Fra4prg/ServoSimulator/pictures/20191102_115943.jpg

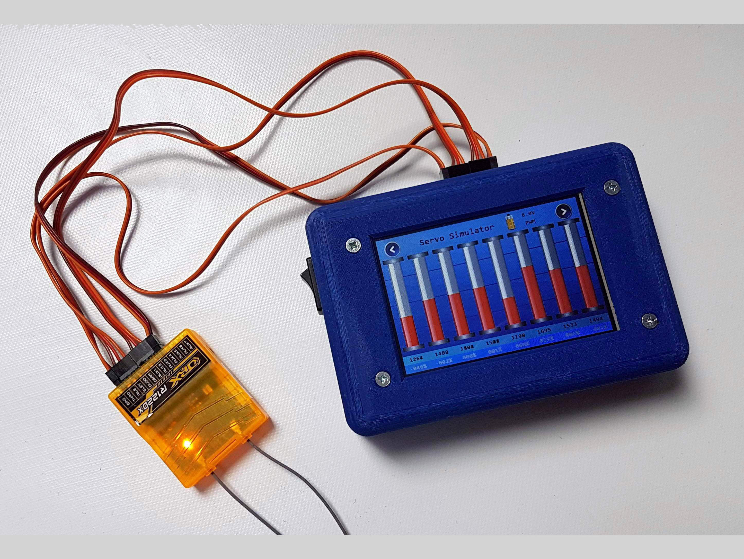
pictures/20191102_115943.jpg
