Fra4prg/ServoSimulator/pictures/20191102_115950.jpg

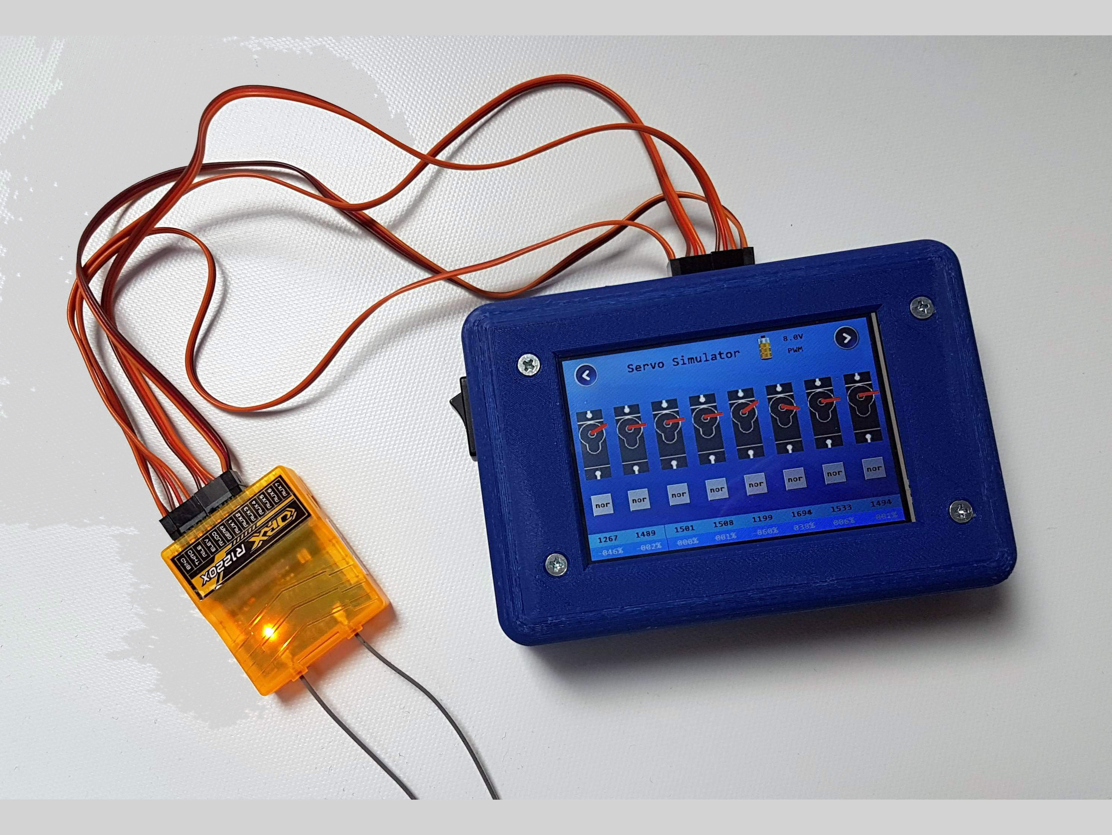
pictures/20191102_115950.jpg
