Fra4prg/ServoSimulator/pictures/20191102_120322.jpg

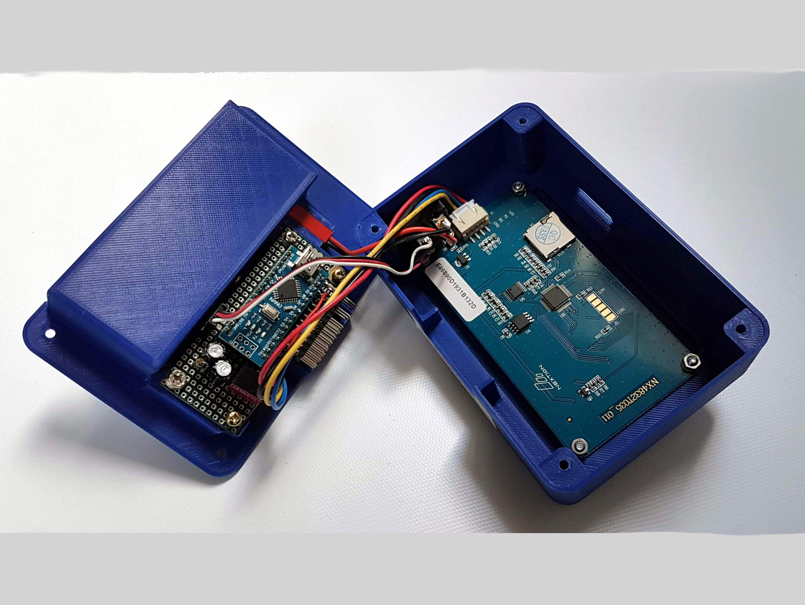
pictures/20191102_120322.jpg
