Fra4prg/ServoSimulator/pictures/20191102_122256.jpg

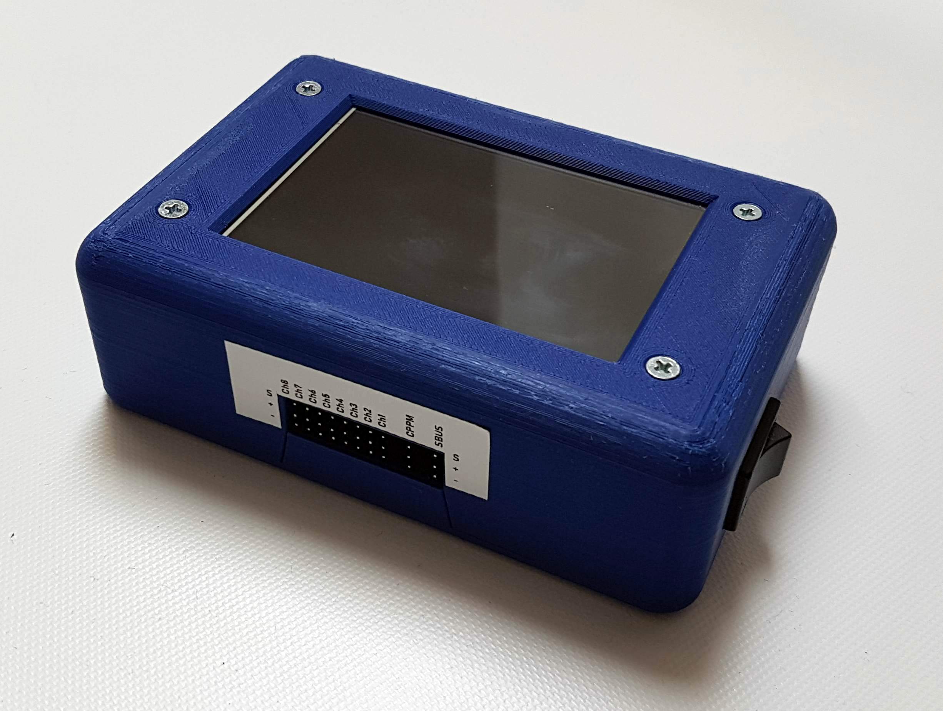
pictures/20191102_122256.jpg
