Fra4prg/ServoSimulator/pictures/20191102_122544.jpg

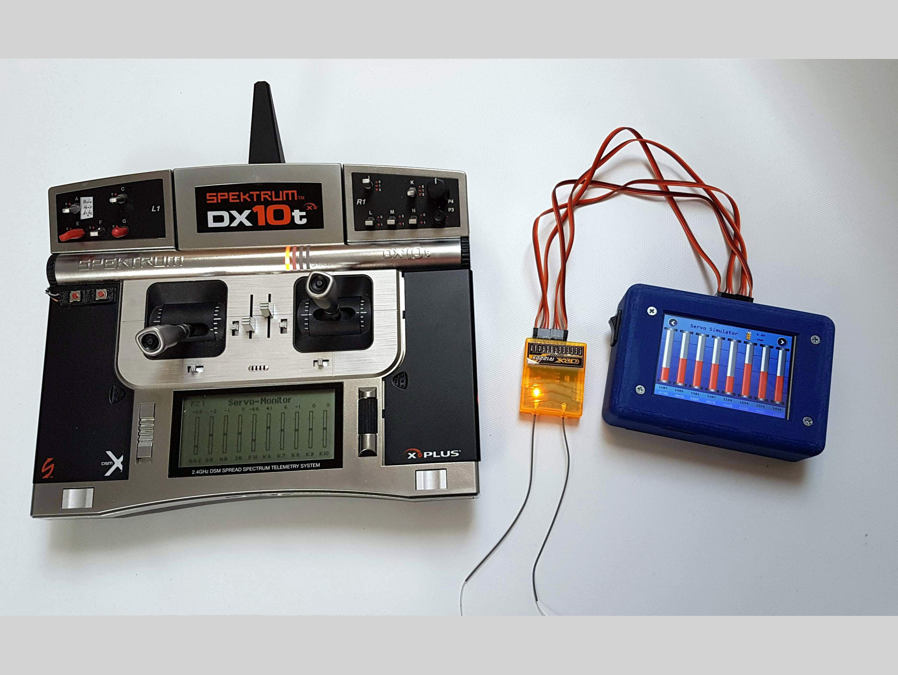
pictures/20191102_122544.jpg
