Fra4prg/ServoSimulator/pictures/20191102_122602.jpg

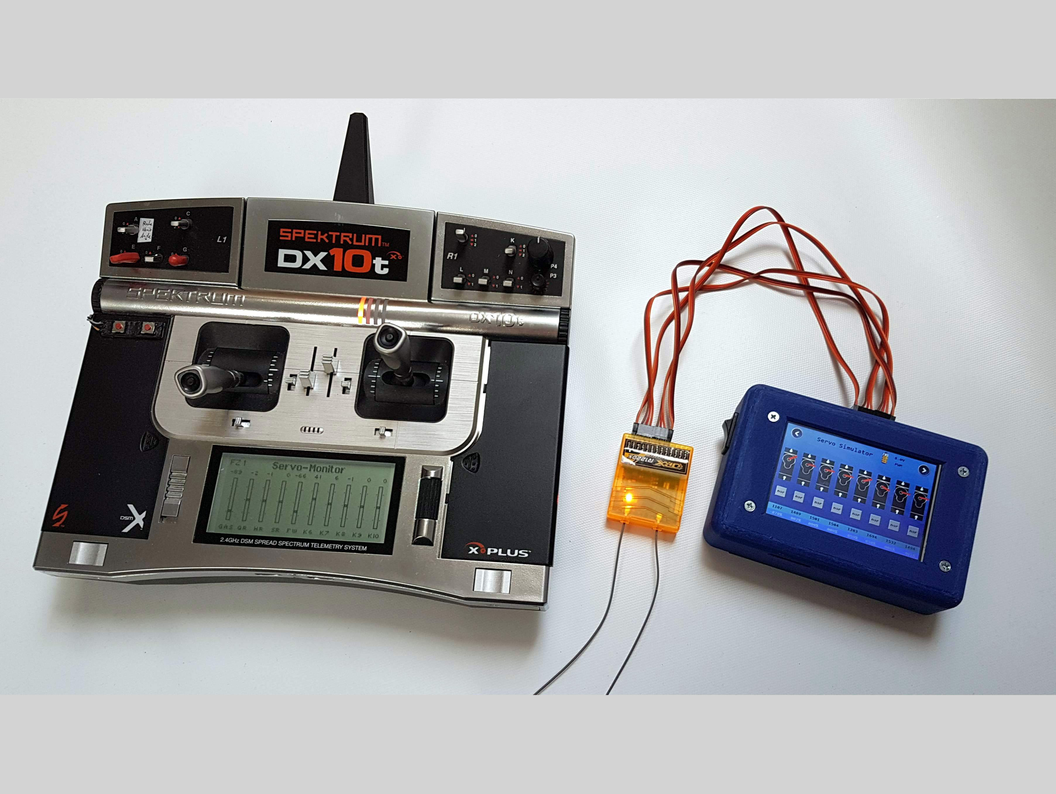
pictures/20191102_122602.jpg
